tanguanhong89/PhasmicKeyboard/diagrams/rows_right.jpg

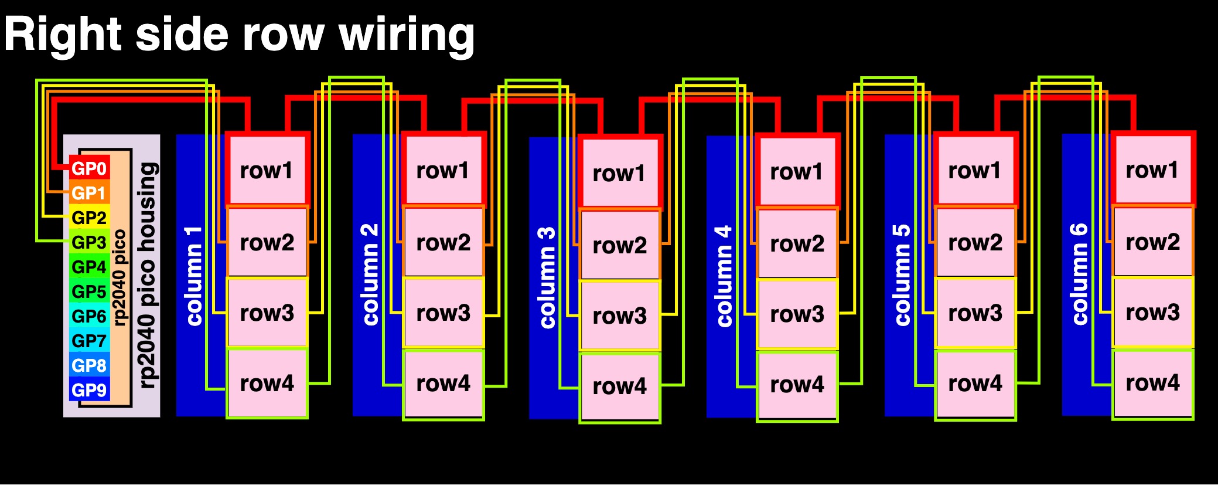
diagrams/rows_right.jpg
