tanguanhong89/PhasmicKeyboard/images/row.jpg

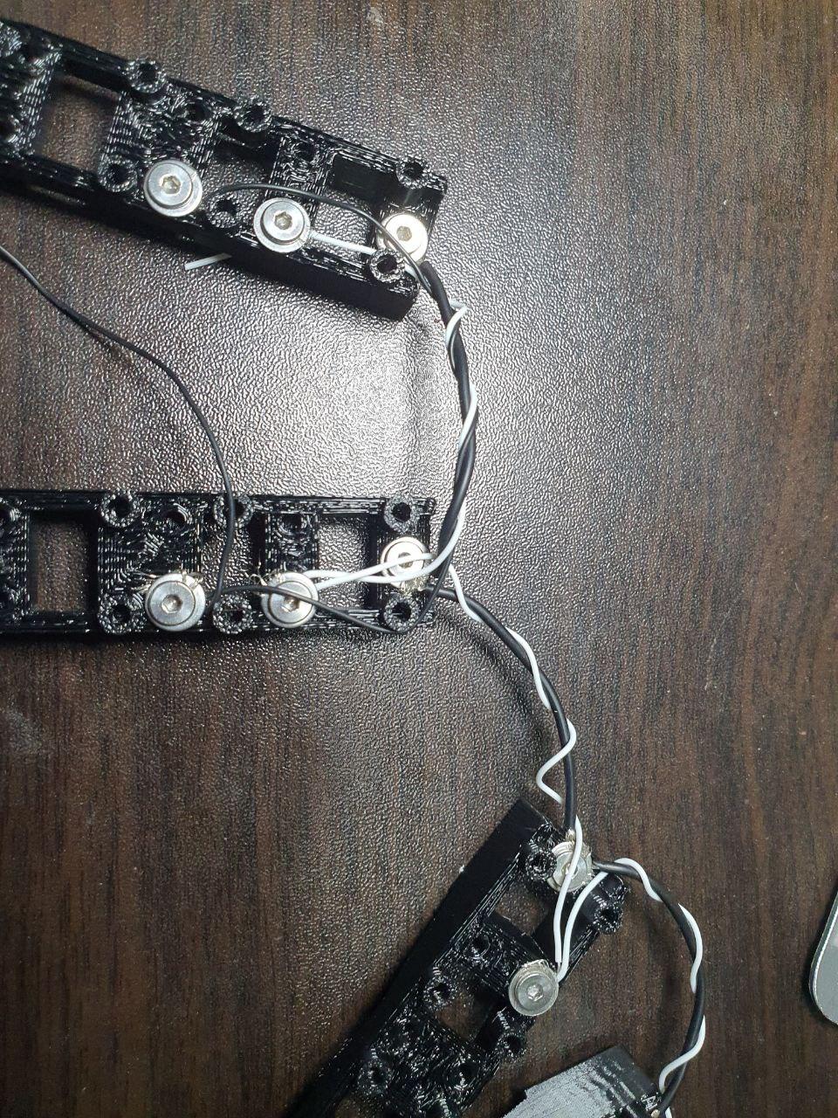
images/row.jpg
