tanguanhong89/PhasmicKeyboard/images/trrs1.jpg

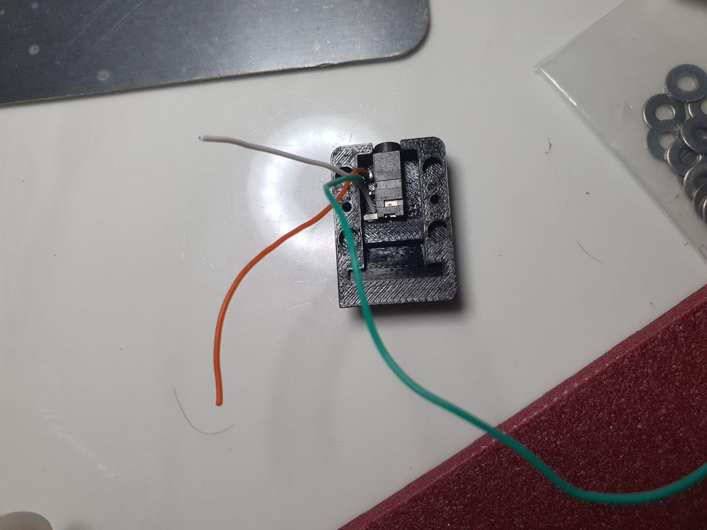
images/trrs1.jpg
